MetrixLambert/Light-Green/CAD files/MoonShotTable/MoonShotTable/box.SLDPRT

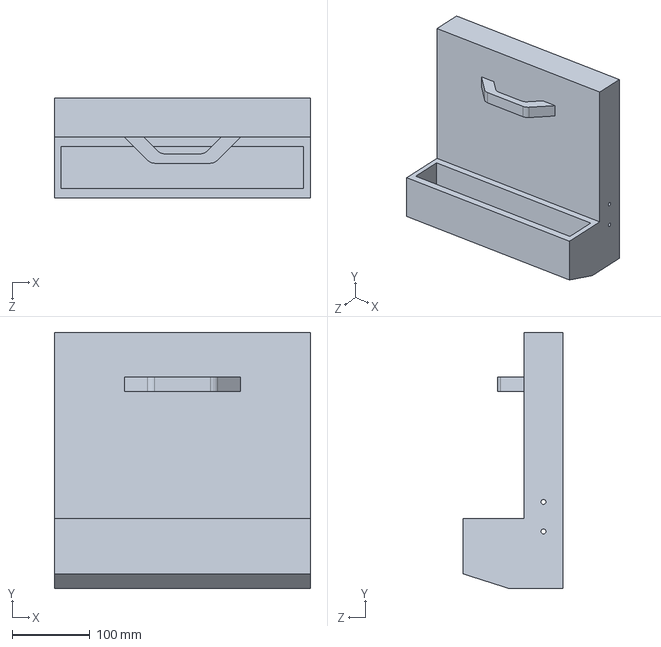
[picture p20: CAD file, 2019-08-04]
CAD files/MoonShotTable/MoonShotTable/box.SLDPRT
330.2 x 330.2 x 129.4 mm
