MetrixLambert/Light-Green/CAD files/partFiles/wheel.SLDPRT

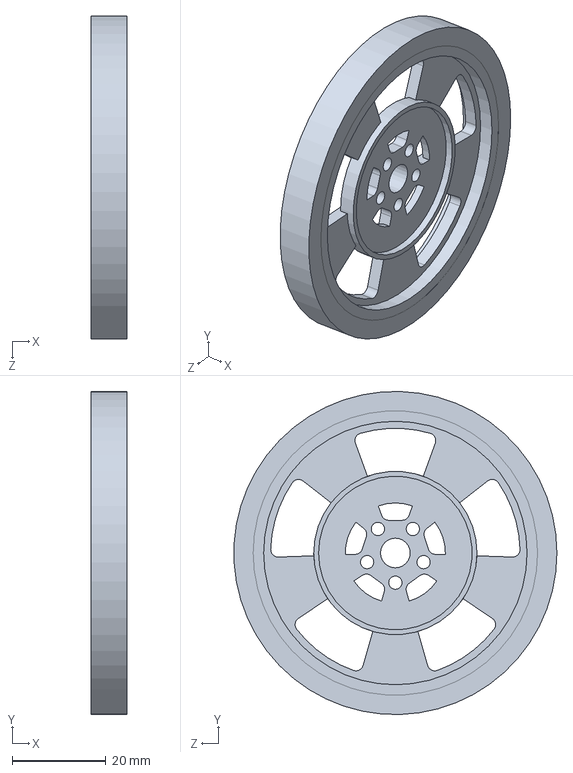
[picture p21: CAD file, 2019-08-04]
CAD files/partFiles/wheel.SLDPRT
7.67 x 69.1 x 69.1 mm
