MetrixLambert/Light-Green/CAD files/roller/roller2.SLDPRT

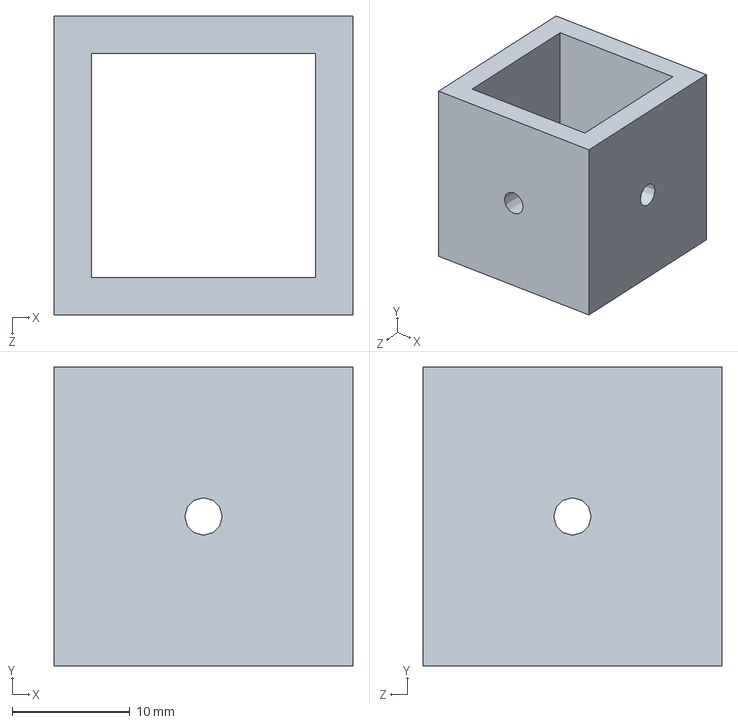
[picture p22: CAD file, 2019-08-04]
CAD files/roller/roller2.SLDPRT
25.4 x 25.4 x 25.4 mm
