MetrixLambert/Light-Green/Lasercutter/plywood T = .125/Trunk 1 (plywood T = .125).DXF

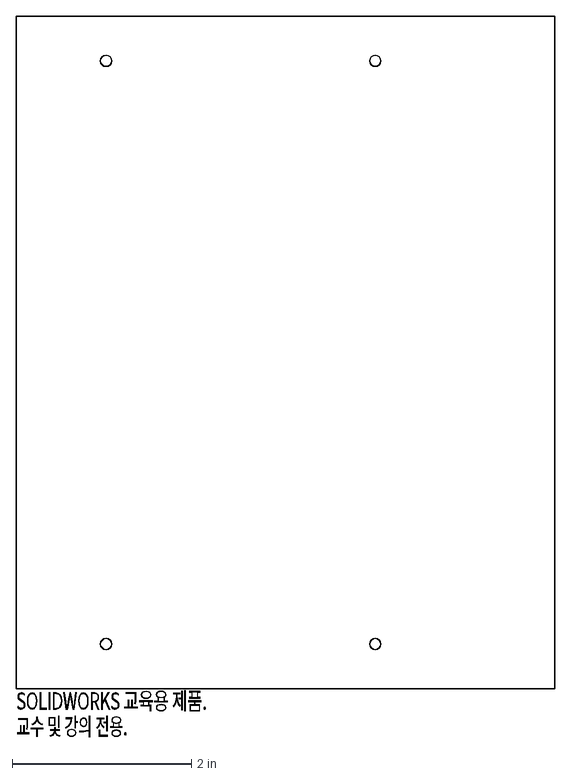
[picture p23: CAD file, 2019-08-04]
Lasercutter/plywood T = .125/Trunk 1 (plywood T = .125).DXF
SOLIDWORKS 교육용 제품.
교수 및 강의 전용.
