MetrixLambert/Light-Green/CAD files/MoonShotTable/MoonShotTable/charger.SLDPRT

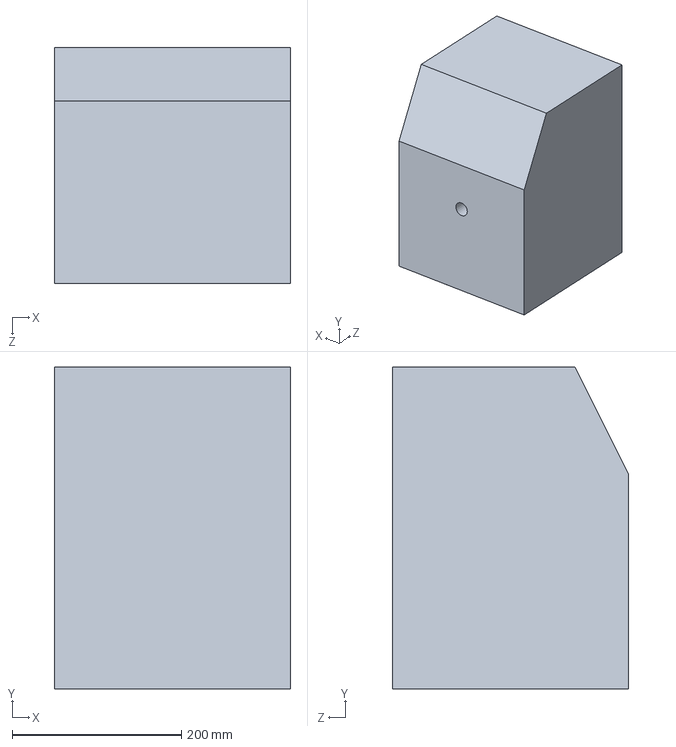
[picture p24: CAD file, 2019-08-04]
CAD files/MoonShotTable/MoonShotTable/charger.SLDPRT
279.4 x 381.0 x 279.4 mm
