MetrixLambert/Light-Green/CAD files/roller/roller3.SLDPRT

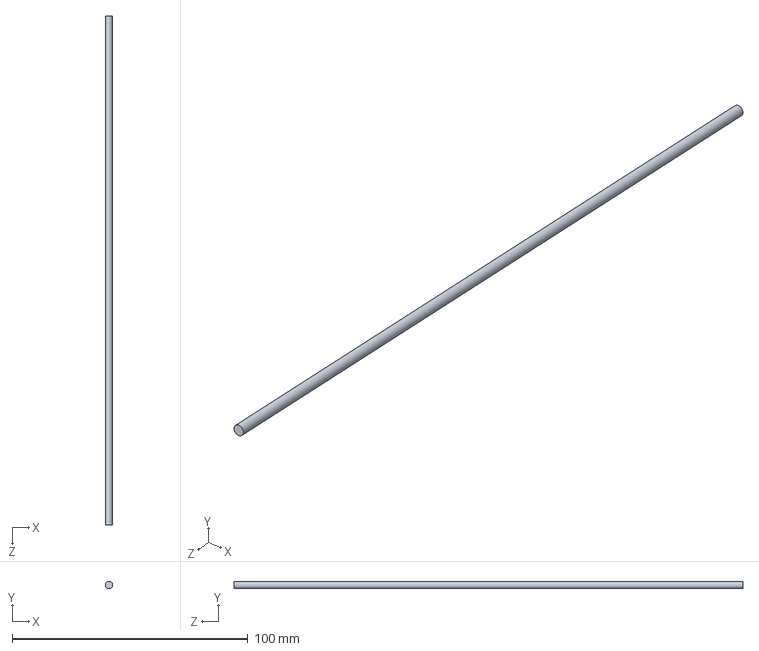
[picture p25: CAD file, 2019-08-04]
CAD files/roller/roller3.SLDPRT
3.17 x 3.17 x 215.9 mm
