MetrixLambert/Light-Green/CAD files/MoonShotTable/MoonShotTable/LEM.SLDPRT

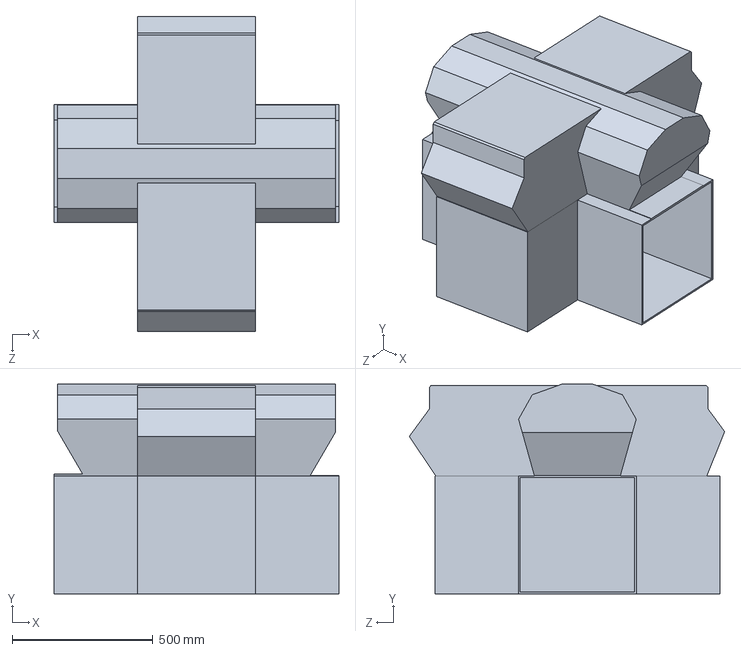
[picture p26: CAD file, 2019-08-04]
CAD files/MoonShotTable/MoonShotTable/LEM.SLDPRT
1010.9 x 744.9 x 1118.7 mm
