MetrixLambert/Light-Green/CAD files/roller/파트7.SLDPRT

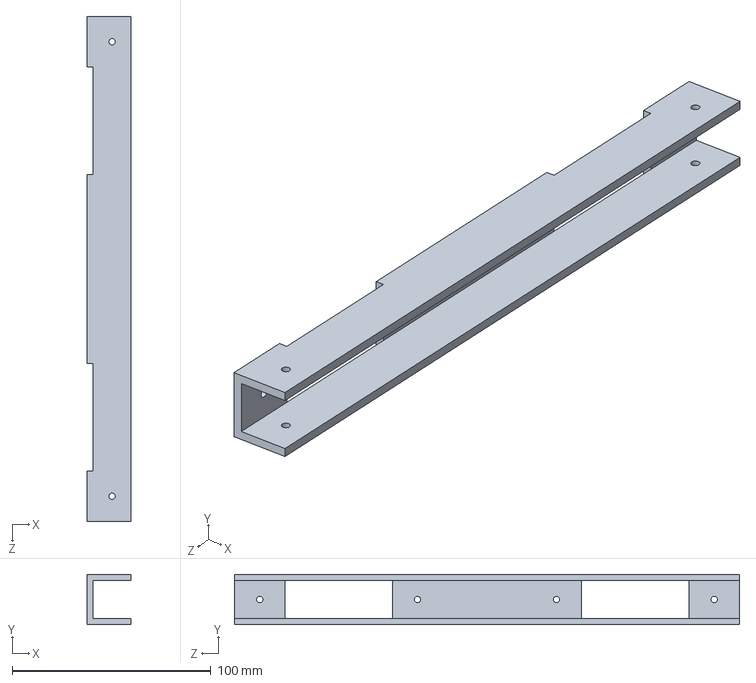
[picture p27: CAD file, 2019-08-04]
CAD files/roller/파트7.SLDPRT
22.2 x 25.4 x 254.0 mm
