MetrixLambert/Light-Green/CAD files/MoonShotTable/MoonShotTable/spinner.SLDPRT

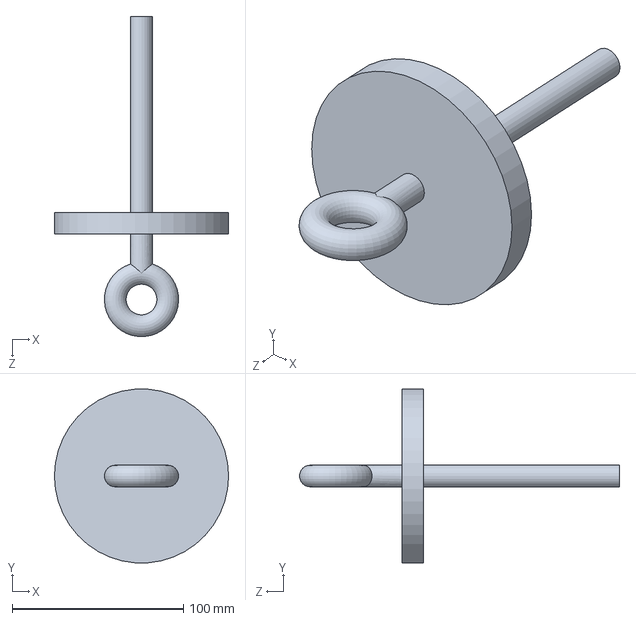
[picture p28: CAD file, 2019-08-04]
CAD files/MoonShotTable/MoonShotTable/spinner.SLDPRT
101.6 x 101.3 x 186.7 mm
