MetrixLambert/Light-Green/CAD files/MoonShotTable/MoonShotTable/lander.SLDPRT

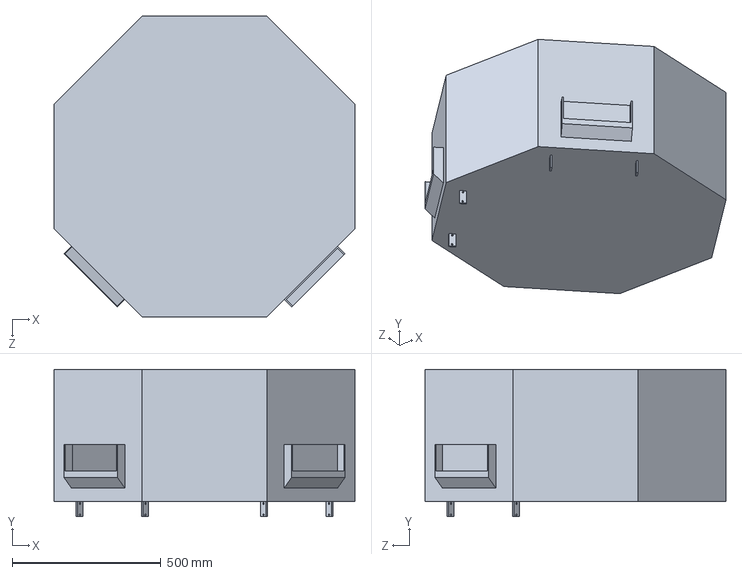
[picture p29: CAD file, 2019-08-04]
CAD files/MoonShotTable/MoonShotTable/lander.SLDPRT
1011.8 x 495.3 x 1011.8 mm
