MetrixLambert/Light-Green/CAD files/MoonShotTable/MoonShotTable/mountain.SLDPRT

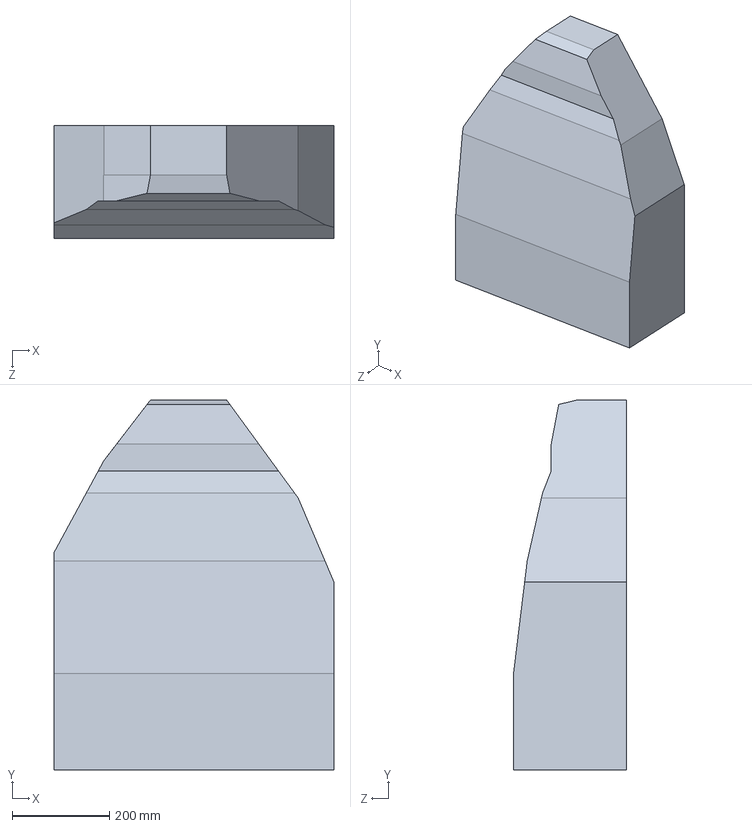
[picture p30: CAD file, 2019-08-04]
CAD files/MoonShotTable/MoonShotTable/mountain.SLDPRT
576.3 x 762.0 x 232.6 mm
