MetrixLambert/Light-Green/CAD files/roller/파트1.SLDPRT

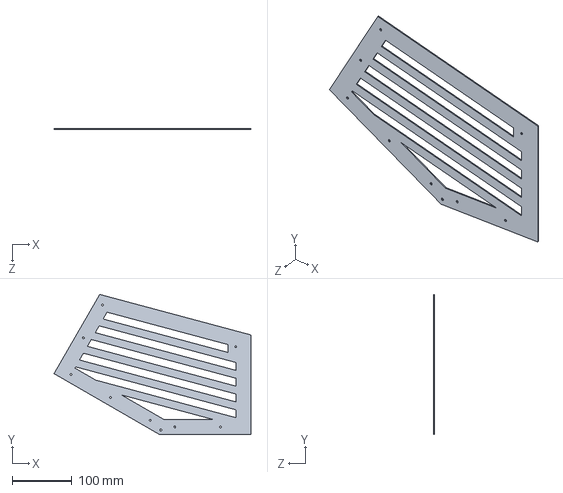
[picture p31: CAD file, 2019-08-04]
CAD files/roller/파트1.SLDPRT
328.4 x 233.6 x 1.59 mm
