MetrixLambert/Light-Green/CAD files/MoonShotTable/MoonShotTable/back.SLDPRT

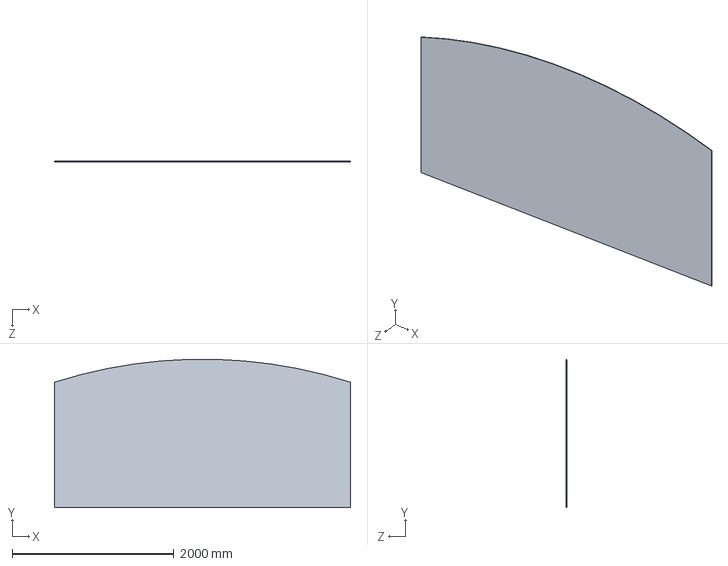
[picture p32: CAD file, 2019-08-04]
CAD files/MoonShotTable/MoonShotTable/back.SLDPRT
3657.6 x 1832.1 x 6.35 mm
