MetrixLambert/Light-Green/CAD files/roller/파트2.SLDPRT

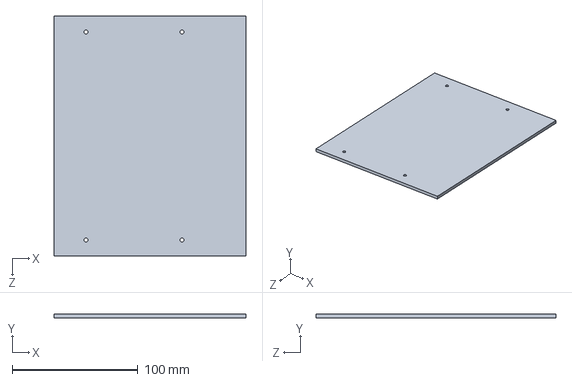
[picture p33: CAD file, 2019-08-04]
CAD files/roller/파트2.SLDPRT
152.4 x 3.17 x 190.5 mm
