MetrixLambert/Light-Green/CAD files/MoonShotTable/MoonShotTable/energy_rod_long.SLDPRT

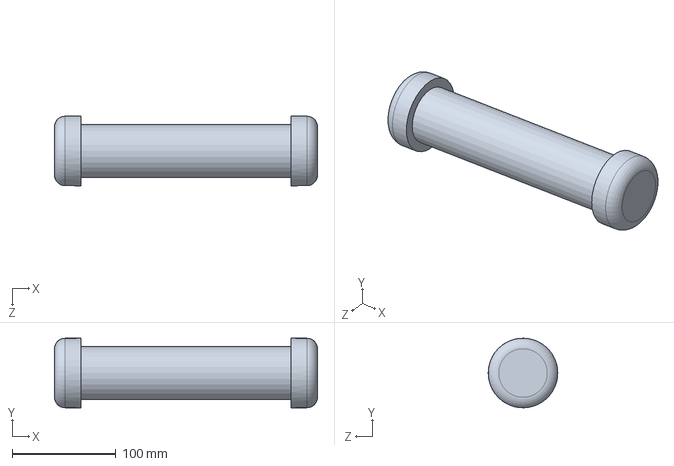
[picture p34: CAD file, 2019-08-04]
CAD files/MoonShotTable/MoonShotTable/energy_rod_long.SLDPRT
254.0 x 67.2 x 67.2 mm
