MetrixLambert/Light-Green/CAD files/roller/파트5.SLDPRT

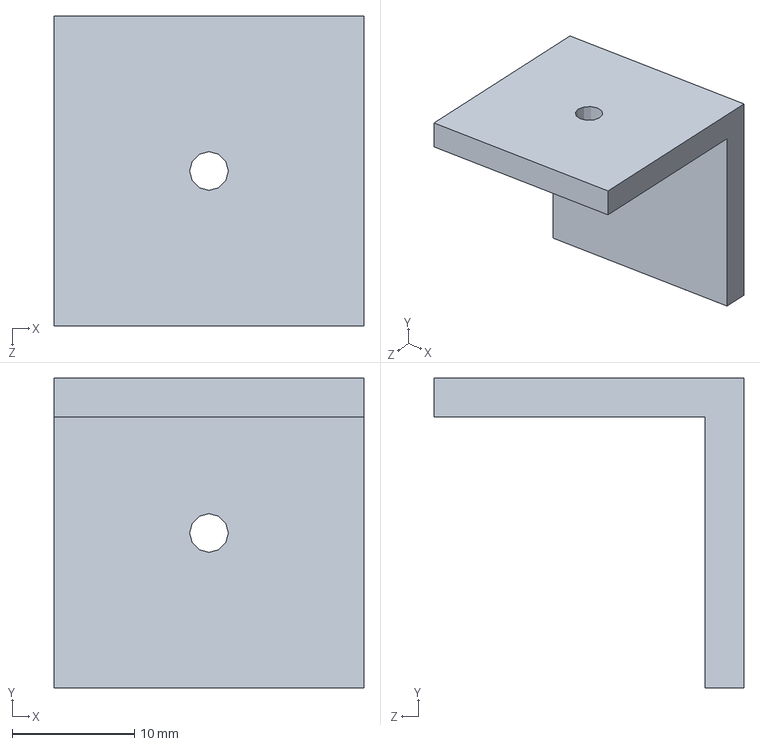
[picture p35: CAD file, 2019-08-04]
CAD files/roller/파트5.SLDPRT
25.4 x 25.4 x 25.4 mm
