MetrixLambert/Light-Green/CAD files/MoonShotTable/MoonShotTable/ramp_right.SLDPRT

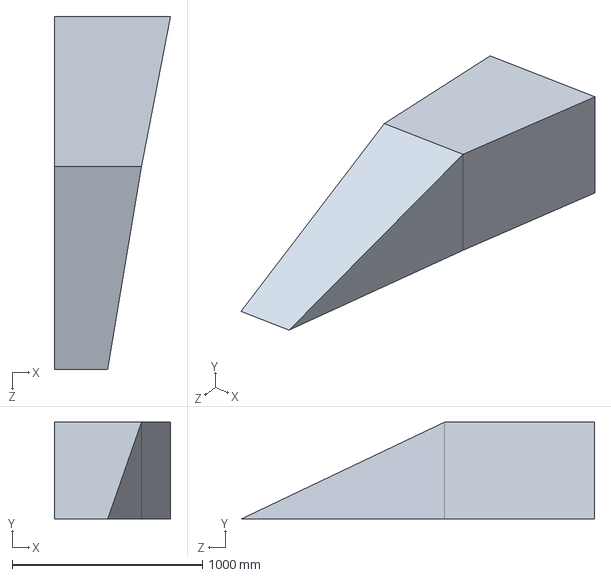
[picture p36: CAD file, 2019-08-04]
CAD files/MoonShotTable/MoonShotTable/ramp_right.SLDPRT
609.6 x 508.0 x 1854.2 mm
