MetrixLambert/Light-Green/CAD files/roller/roller1.SLDPRT

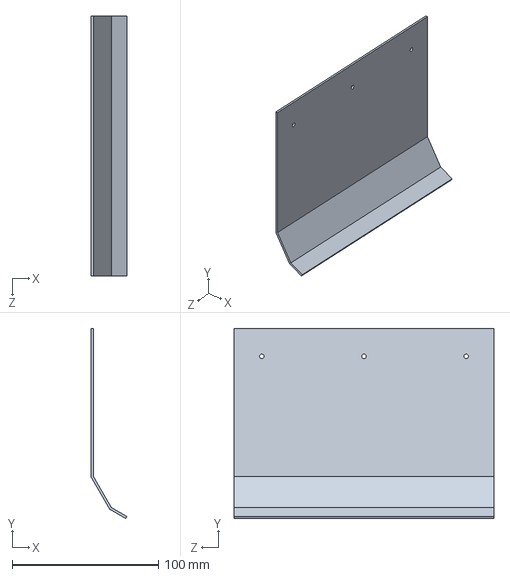
[picture p37: CAD file, 2019-08-04]
CAD files/roller/roller1.SLDPRT
24.5 x 129.9 x 177.8 mm
