MetrixLambert/Light-Green/CAD files/MoonShotTable/MoonShotTable/ramp_left.SLDPRT

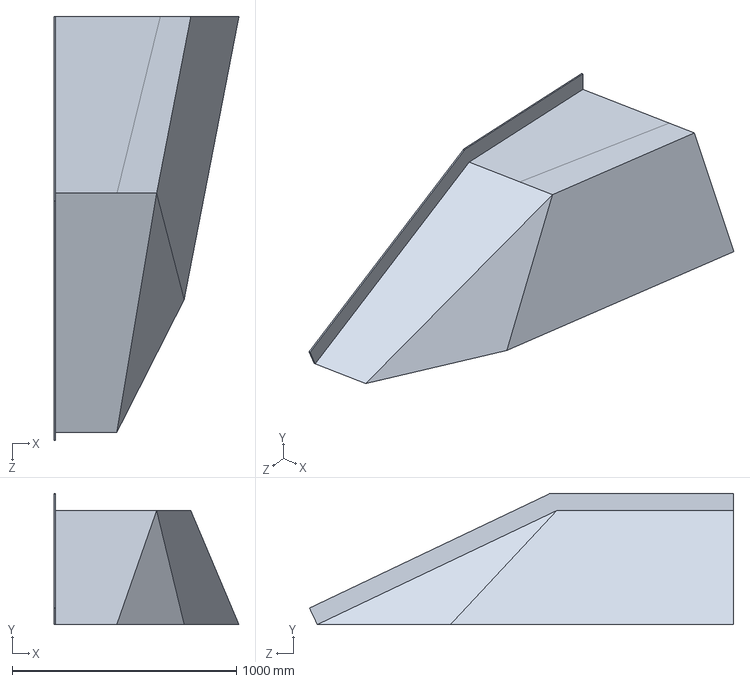
[picture p38: CAD file, 2019-08-04]
CAD files/MoonShotTable/MoonShotTable/ramp_left.SLDPRT
824.2 x 584.2 x 1889.1 mm
