MetrixLambert/Light-Green/CAD files/MoonShotTable/MoonShotTable/leg.SLDPRT

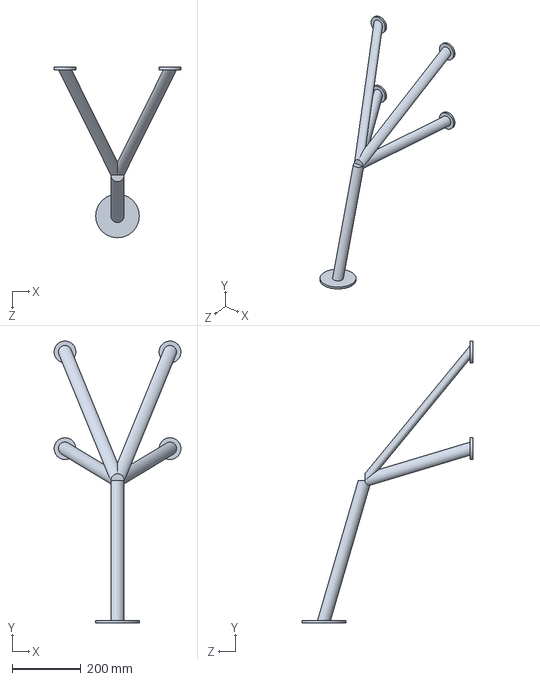
[picture p39: CAD file, 2019-08-04]
CAD files/MoonShotTable/MoonShotTable/leg.SLDPRT
368.3 x 818.4 x 495.3 mm
