MetrixLambert/Light-Green/CAD files/MoonShotTable/MoonShotTable/base.SLDPRT

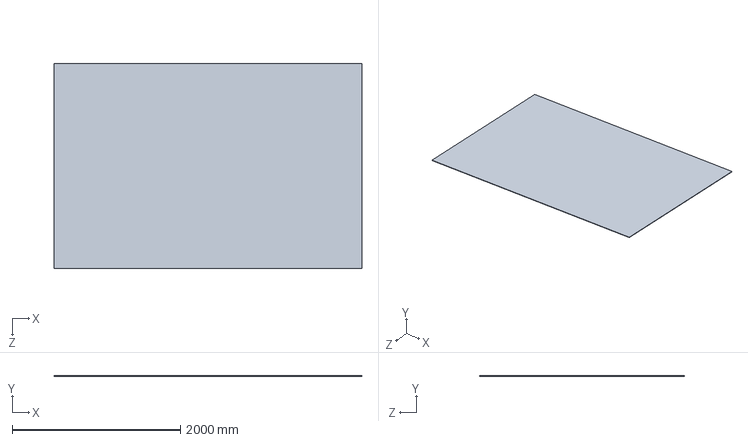
[picture p41: CAD file, 2019-08-04]
CAD files/MoonShotTable/MoonShotTable/base.SLDPRT
3657.6 x 6.35 x 2438.4 mm
