MetrixLambert/Light-Green/CAD files/MoonShotTable/MoonShotTable/bridge.SLDPRT

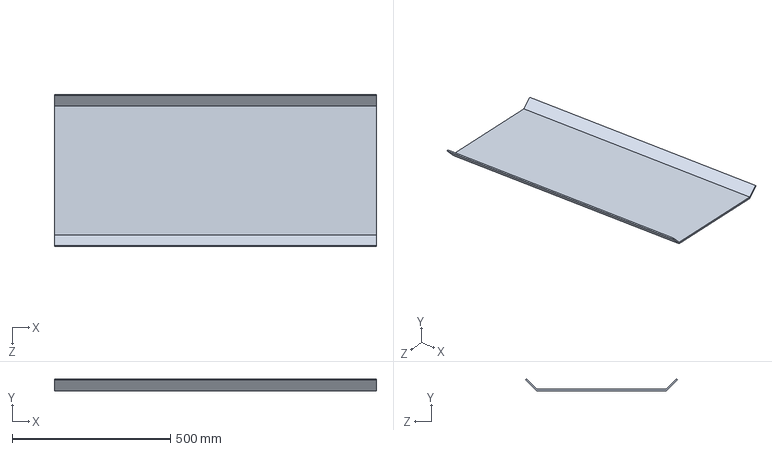
[picture p42: CAD file, 2019-08-04]
CAD files/MoonShotTable/MoonShotTable/bridge.SLDPRT
1016.0 x 38.7 x 479.2 mm
